ikechangexentrick/function_generator/function_generator/function_generator_ui.cpp

#include "function_generator_ui.h"
#include "Display_OLED.h"

#include "euclidean.h"

static constexpr size_t N_CH = 4096;

extern Application *app;
extern MenuApp app_menu;
extern Display_OLED display;

extern ChannelApp app_channel;
extern ChannelApp app_cv_channel;

extern FreqApp app_freq;

extern SrcApp app_src;
extern MultApp app_mult;
extern PhaseApp app_phase;

extern FuncApp app_func;
extern ARE_Attack_App app_func_are_attack;
extern ARE_Release_App app_func_are_release;

extern PolarityApp app_pol;

extern PatternController ptnctl;
extern Euclid_Len_App app_euc_len;
extern Euclid_Num_App app_euc_num;
extern Euclid_Sft_App app_euc_sft;

void FreqApp::set_sync_mode(size_t ch, SyncType type)
{
	auto &flag = data[ch].sync_flag;
	flag = type;
	register_update();
}

void FreqApp::set_free_mode(size_t ch)
{
	auto &flag = data[ch].sync_flag;
	flag = Free;
	register_update();
}

bool FreqApp::check_new_period(size_t ch, unsigned long t)
{
	bool ret = false;
	unsigned long cur_phase = 0;

	if (sync_mode(ch) != Free) {
		auto coeff = app_mult.get_coeff(ch);
		auto factor = app_phase.get_factor(ch);
		auto freq = get_frequency(ch);
		cur_phase = (t - (unsigned long)(1e6/freq/8.0*factor)) % (unsigned long)(1e6/freq/coeff);
	} else {
		cur_phase = t % (unsigned long)(1e6/get_frequency(ch));
	}

	if (cur_phase < data[ch].prev_phase) ret = true;
	data[ch].prev_phase = cur_phase;
	return ret;
}

void FreqApp::onButton(int state)
{
	if (state == 1) {
		app = &app_menu;

		display.show_app_msg(" ");
		display.show_menu(app_menu.get_current()->get_title());
	}
}

void FreqApp::onRotarySW(RotarySwitch::RSW_DIR dir)
{
	const auto ch = app_channel.get_current_channel();

	if (freq_mode == FREQ_MODE) {
		auto &freq = data[ch].freq;
		if (dir == RotarySwitch::CW) {
			if (freq < 1) {
				freq *= 1.2;
			} else {
				freq += 1;
			}

		} else {
			if (freq <= 1) {
				freq /= 1.2;
			} else {
				freq -= 1;
			}

		}

		display.show_app_msg("   %5.1f", freq);
	} else if (freq_mode == BPM_MODE) {
		size_t bpm = (size_t)(60.0*data[ch].freq);
		if (dir == RotarySwitch::CW) {
			bpm += 1;

		} else {
			if (bpm > 0) {
				bpm -= 1;
			}

		}

		display.show_app_msg("   %3d", bpm);
		data[ch].freq = (double)bpm/60.0;
	} else {
		// never reach here
	}
	register_update();
}

void FreqApp::apply_cv(size_t ch, size_t cv)
{
	auto &freq = data[ch].freq;

	// 0.03 - 30 Hz / -1.5 - 1.5
	auto new_value = pow(10.0, -1.5 + (1.5 - (-1.5))*(double)cv/1024.0);
	freq = new_value;
}

void FreqApp::set_param(size_t ch, double f, unsigned long p)
{
		auto coeff = app_mult.get_coeff(ch);
		if (coeff >= 1) {
			auto &ext_freq = data[ch].ext_freq;
			auto &ext_phase = data[ch].ext_phase;
			ext_freq = f;
			ext_phase = p;
		} else {
			if (data[ch].phase_counter >= 1.0/coeff-1) {
				data[ch].phase_counter = 0;
				auto &ext_freq = data[ch].ext_freq;
				auto &ext_phase = data[ch].ext_phase;
				ext_freq = f;
				ext_phase = p;
			}
			data[ch].phase_counter += 1;
		}
}

void FuncApp::onButton(int state)
{
	if (state == 1) {
		app = &app_menu;

		display.show_app_msg(" ");
		display.show_menu(app_menu.get_current()->get_title());
	}
}

double func_sin(unsigned long t, double freq, unsigned long phase)
{
	return sin( 2*3.141592*freq/1e6*(t - phase) );
}

double func_saw(unsigned long t, double freq, unsigned long phase)
{
	auto lambda = (1e6/freq); // in us
	auto out = (N_CH-1)/lambda * (double)( (t-phase) % (unsigned long)lambda );
	return out;
}

double func_tri(unsigned long t, double freq, unsigned long phase)
{
	auto saw2 = func_saw(t, freq, phase)*2;
	if (saw2 > (N_CH-1)) return (N_CH-1)*2-saw2;
	else return saw2;
}

double func_sq(unsigned long t, double freq, unsigned long phase)
{
	auto saw = func_saw(t, freq, phase);
	return (saw < N_CH/2) ? (N_CH-1) : 0;
}

double func_are(unsigned long t, double freq, unsigned long phase, unsigned long attack, unsigned long release)
{
	auto lambda = (1e6/freq); // in us
	auto l_attack = lambda*attack/100;
	auto l_release = lambda*release/100;

	auto dt = (t-phase) % (unsigned long)lambda;
	if (dt <= l_attack) return (N_CH-1)/l_attack * (double)dt;
	else if (dt <= l_attack+l_release) return (N_CH-1) -(N_CH-1)/l_release * (double)(dt - l_attack);
	else return 0.0;
}

void FuncApp::onRotarySW(RotarySwitch::RSW_DIR dir)
{
	const auto ch = app_channel.get_current_channel();
	auto &idx = data[ch].idx;
	if (dir == RotarySwitch::CW) {
		if (idx < FUNC_MAX-1) idx += 1;

	} else {
		if (idx > 0) idx -= 1;

	}

	display.show_app_msg("   %s", get_func_name(ch));
	register_update();
}

auto FuncApp::get_function(size_t ch) const -> std::function<double(unsigned long, double, unsigned long)>
{
	const auto &idx = data[ch].idx;

	if (idx == SIN) {
		return [=](unsigned long t, double f, unsigned long p) { return (func_sin(
			t, f, p)+1)/2*(N_CH-1); };
	} else if (idx == SAW_TOOTH) {
		return [=](unsigned long t, double f, unsigned long p) { return func_saw(
			t, f, p); };
	} else if (idx == TRIANGLE) {
		return [=](unsigned long t, double f, unsigned long p) { return func_tri(
			t, f, p); };
	} else if (idx == SQUARE) {
		return [=](unsigned long t, double f, unsigned long p) { return func_sq(
			t, f, p); };
	} else if (idx == AR_ENVELOPE) {
		return [=](unsigned long t, double f, unsigned long p) { return func_are(
			t, f, p, app_func_are_attack.get_value(ch), app_func_are_release.get_value(ch)); };
	}

	return std::function<long(unsigned long, double, unsigned long)>();
}

void FuncApp::apply_cv(size_t ch, size_t cv)
{
	auto &idx = data[ch].idx;

	// 0 - FUNC_MAX-1
	idx = (int)(((double)cv/1024.0)*(double)FUNC_MAX);
}

//  -----------------------------------------------

void ChannelApp::onButton(int state)
{
	if (state == 1) {
		app = &app_menu;

		display.show_app_msg(" ");
		display.show_menu(app_menu.get_current()->get_title());
	}
}

void ChannelApp::onRotarySW(RotarySwitch::RSW_DIR dir)
{
	if (dir == RotarySwitch::CW) {
		if (ch < ChannelMax-1) ch += 1;

	} else {
		if (ch > 0) ch -= 1;

	}

	display.show_app_msg("   %u", get_current_channel()+1);
	register_update();
}

//  -----------------------------------------------

void SrcApp::onButton(int state)
{
	if (state == 1) {
		app = &app_menu;

		display.show_app_msg(" ");
		display.show_menu(app_menu.get_current()->get_title());
	}
}

void SrcApp::onRotarySW(RotarySwitch::RSW_DIR dir)
{
	const size_t ch = app_channel.get_current_channel();
	int type = (int)type_print[ch];

	if (dir == RotarySwitch::CW) {
		if (type < FreqApp::Sync_ExtClock) {
			type += 1;
		}
	} else {
		if (type > FreqApp::Sync_Channel1) {
			type -= 1;
		}
	}
	type_print[ch] = (FreqApp::SyncType)type;

	// check if the master channel is external or free or not the channel itself
	if (ch == type || (type < ChannelApp::ChannelMax && app_freq.sync_mode(type) != FreqApp::Free)) {
		display.show_app_msg("   -");
	} else {
		app_freq.set_sync_mode(ch, (FreqApp::SyncType)type);
		display.show_app_msg("   %s", get_source_name((FreqApp::SyncType)type));
	}
	register_update();
}

const char *get_source_name(FreqApp::SyncType type)
{
	if (type == FreqApp::Sync_Channel1) return "ch1";
	else if (type == FreqApp::Sync_Channel2) return "ch2";
	else if (type == FreqApp::Sync_Channel3) return "ch3";
	else if (type == FreqApp::Sync_Channel4) return "ch4";
	else if (type == FreqApp::Sync_Channel5) return "ch5";
	else if (type == FreqApp::Sync_Channel6) return "ch6";
	else if (type == FreqApp::Sync_Channel7) return "ch7";
	else if (type == FreqApp::Sync_Channel8) return "ch8";
	else if (type == FreqApp::Sync_ExtClock) return "clk";
	else return "free";
}

//  -----------------------------------------------

void MultApp::onButton(int state)
{
	if (state == 1) {
		app = &app_menu;

		display.show_app_msg(" ");
		display.show_menu(app_menu.get_current()->get_title());
	}
}

void MultApp::onRotarySW(RotarySwitch::RSW_DIR dir)
{
	const size_t ch = app_channel.get_current_channel();
	auto &sign = data[ch].sign;
	auto &factor = data[ch].factor;

	if (dir == RotarySwitch::CW) {
		if (sign == Mult) {
			factor += 1;
		} else if (sign == Eq) {
			factor += 1;
			sign = Mult;
		} else {
			factor -= 1;
			if (factor == 1) {
				sign = Eq;
			}
		}

	} else {
		if (sign == Div) {
			factor += 1;
		} else if (sign == Eq) {
			factor += 1;
			sign = Div;
		} else {
			factor -= 1;
			if (factor == 1) {
				sign = Eq;
			}
		}

	}

	display.show_app_msg("   %s%d", get_sign(ch), get_factor(ch));
	register_update();
}

void MultApp::apply_cv(size_t ch, size_t cv)
{
	auto &factor = data[ch].factor;
	auto &sign = data[ch].sign;

	// /10 - *10
	auto x = (double)(cv-512)/1024.0;
	if (x >= -0.05 || x <= 0.05) {
		sign = Eq;
		factor = 1;
	} else if (x > 0.05) {
		sign = Mult;
		factor = (int)(x*20);
	} else if (x < -0.05) {
		sign = Div;
		factor = (int)(-x*20);
	}
}

double MultApp::get_coeff(size_t ch) const
{
	const auto &sign = data[ch].sign;
	const auto &factor = data[ch].factor;
	if (sign == Mult || sign == Eq) return factor;
	else return 1.0/factor;
}

//  -----------------------------------------------

void PhaseApp::onButton(int state)
{
	if (state == 1) {
		app = &app_menu;

		display.show_app_msg(" ");
		display.show_menu(app_menu.get_current()->get_title());
	}
}

void PhaseApp::onRotarySW(RotarySwitch::RSW_DIR dir)
{
	const size_t ch = app_channel.get_current_channel();
	auto &factor = data[ch].factor;

	if (dir == RotarySwitch::CW) {
		if (factor < 8) factor += 1;

	} else {
		if (factor > 0) factor -= 1;

	}

	display.show_app_msg("   %d", get_factor(ch));
	register_update();
}

void PhaseApp::apply_cv(size_t ch, size_t cv)
{
	auto &factor = data[ch].factor;

	// 0 - 8
	factor = (int)((double)cv/1024.0*8);
}

//  -----------------------------------------------

void ARE_Attack_App::onButton(int state)
{
	if (state == 1) {
		app = &app_menu;

		display.show_app_msg(" ");
		display.show_menu(app_menu.get_current()->get_title());
	}
}

void ARE_Attack_App::onRotarySW(RotarySwitch::RSW_DIR dir)
{
	const size_t ch = app_channel.get_current_channel();
	auto &value = data[ch].value;
	const auto &release = app_func_are_release.get_value(ch);

	if (dir == RotarySwitch::CW) {
		if (value + release < 100) value += 1;
	} else {
		if (value > 1) value -= 1;
	}

	display.show_app_msg("   %d", value);
	register_update();
}

void ARE_Attack_App::apply_cv(size_t ch, size_t cv)
{
	auto &value = data[ch].value;

	// 0 - 100-release
	const auto release = app_func_are_release.get_value(ch);
	value = (double)cv/1024.0*(double)(100-release);
}

void ARE_Release_App::onButton(int state)
{
	if (state == 1) {
		app = &app_menu;

		display.show_app_msg(" ");
		display.show_menu(app_menu.get_current()->get_title());
	}
}

void ARE_Release_App::onRotarySW(RotarySwitch::RSW_DIR dir)
{
	const size_t ch = app_channel.get_current_channel();
	auto &value = data[ch].value;
	const auto &attack = app_func_are_attack.get_value(ch);

	if (dir == RotarySwitch::CW) {
		if (value + attack < 100) value += 1;
	} else {
		if (value > 1) value -= 1;
	}

	display.show_app_msg("   %d", value);
	register_update();
}

void ARE_Release_App::apply_cv(size_t ch, size_t cv)
{
	auto &value = data[ch].value;

	// 0 - 100-attack
	const auto attack = app_func_are_attack.get_value(ch);
	value = (double)cv/1024.0*(double)(100-attack);
}

//  -----------------------------------------------

void PolarityApp::onButton(int state)
{
	if (state == 1) {
		app = &app_menu;

		display.show_app_msg(" ");
		display.show_menu(app_menu.get_current()->get_title());
	}
}

void PolarityApp::onRotarySW(RotarySwitch::RSW_DIR dir)
{
	const size_t ch = app_channel.get_current_channel();
	auto &value = data[ch].mode;

	if (dir == RotarySwitch::CW) {
		if (value == Unipolar) value = Bipolar;
	} else {
		if (value == Bipolar) value = Unipolar;
	}

	display.show_app_msg("   %s", get_mode_msg(ch));
	register_update();
}


//  -----------------------------------------------

void PatternController::notify(size_t ch)
{
	auto type = data[ch].type;

	if (type == Off) {
		data[ch].enabled = true;
	} else if (type == Euclidean) {

		const auto len = app_euc_len.get_value(ch);

		auto &cnt = data[ch].euc_cnt;
		int *ptn = data[ch].euc_pattern;
		if (cnt == 0) {
			auto num = app_euc_num.get_value(ch);
			auto sft = app_euc_sft.get_value(ch);
			if (num > len) {
				num = len;
				app_euc_num.set_value(ch, num);
			}
			if (sft > len) {
				sft = len;
				app_euc_sft.set_value(ch, sft);
			}
			euclidean(num, sft, ptn, len);
		}

		if (ptn[cnt]) data[ch].enabled = true;
		else data[ch].enabled = false;

		if (++cnt >= len) cnt = 0;
	}
}

bool PatternController::enabled(size_t ch) const
{
	return data[ch].enabled;
}

void PatternController::get_msg(size_t ch, char *p, size_t len)
{
	if (data[ch].type == Off) {
		snprintf(p, len, "  ptn:off");
	} else if (data[ch].type == Euclidean) {
		snprintf(p, len, "  ptn:Euc:%d/%d/%d", app_euc_len.get_value(ch), app_euc_num.get_value(ch), app_euc_sft.get_value(ch));
	}
}

void Euclid_Len_App::onButton(int state)
{
	if (state == 1) {
		app = &app_menu;

		display.show_app_msg(" ");
		display.show_menu(app_menu.get_current()->get_title());
	}
}

void Euclid_Len_App::onRotarySW(RotarySwitch::RSW_DIR dir)
{
	const size_t ch = app_channel.get_current_channel();
	auto &value = data[ch].value;

	if (dir == RotarySwitch::CW) {
		if (value < MAX_LEN) value += 1;
	} else {
		if (value > 1) value -= 1;
	}

	display.show_app_msg("   %d", value);
	register_update();
}

void Euclid_Len_App::apply_cv(size_t ch, size_t cv)
{
	auto &value = data[ch].value;

	// 1 - MAX_LEN-1
	value = (int)((double)cv/1024.0*(double)(MAX_LEN-1)) +1;
}

void Euclid_Num_App::onButton(int state)
{
	if (state == 1) {
		app = &app_menu;

		display.show_app_msg(" ");
		display.show_menu(app_menu.get_current()->get_title());
	}
}

void Euclid_Num_App::onRotarySW(RotarySwitch::RSW_DIR dir)
{
	const size_t ch = app_channel.get_current_channel();
	auto &value = data[ch].value;
	const auto len = app_euc_len.get_value(ch);

	if (dir == RotarySwitch::CW) {
		if (value < len) value += 1;
	} else {
		if (value > 0) value -= 1;
	}

	display.show_app_msg("   %d", value);
	register_update();
}

void Euclid_Num_App::apply_cv(size_t ch, size_t cv)
{
	auto &value = data[ch].value;

	// 0 - len
	const auto len = app_euc_len.get_value(ch);
	value = (int)((double)cv/1024.0*(double)len);
}

void Euclid_Sft_App::onButton(int state)
{
	if (state == 1) {
		app = &app_menu;

		display.show_app_msg(" ");
		display.show_menu(app_menu.get_current()->get_title());
	}
}

void Euclid_Sft_App::onRotarySW(RotarySwitch::RSW_DIR dir)
{
	const size_t ch = app_channel.get_current_channel();
	auto &value = data[ch].value;
	const auto len = app_euc_len.get_value(ch);

	if (dir == RotarySwitch::CW) {
		if (value < len) value += 1;
	} else {
		if (value > 0) value -= 1;
	}

	display.show_app_msg("   %d", value);
	register_update();
}

void Euclid_Sft_App::apply_cv(size_t ch, size_t cv)
{
	auto &value = data[ch].value;

	// 0 - len
	const auto len = app_euc_len.get_value(ch);
	value = (int)((double)cv/1024.0*(double)len);
}


template class CVApp<11>;

template <int N>
void CVApp<N>::onButton(int state)
{
	if (state == 1) {

		if (this->idx == this->titles.size()-1) /* Back */ {
			app = &app_menu;

			display.show_app_msg(" ");
			display.show_menu(app_menu.get_current()->get_title());

		} else {
			this->selected = this->idx;
			this->callbacks[this->idx]();

		}
	}
}

template <int N>
void CVApp<N>::onRotarySW(RotarySwitch::RSW_DIR dir)
{
	if (dir == RotarySwitch::CW) {
		if (this->idx < this->titles.size()-1) this->idx += 1;
	} else {
		if (this->idx > 0) this->idx -= 1;
	}

	const auto &item = this->titles[this->idx].c_str();

	if (this->idx == this->titles.size()-1) {
		display.show_app_msg("   <%s", item);
	} else {
		display.show_app_msg("   [%s]", item);
	}
	register_update();
}

template <int N>
void CVApp<N>::get_app_msg(char *p, size_t len)
{
	memcpy(p, &this->titles[this->selected][0], len);
}

//  -----------------------------------------------

void Menu_Channel::exec()
{
	display.show_app_msg("   %u", app_channel.get_current_channel()+1);
	app = &app_channel;
}


void Menu_Free::exec()
{
	const size_t ch = app_channel.get_current_channel();
	app_freq.set_free_mode(ch);
}

void Menu_Freq::exec()
{
	const size_t ch = app_channel.get_current_channel();
	display.show_app_msg("   %5.1f", app_freq.get_frequency(ch));
	app_freq.set_mode(FreqApp::FREQ_MODE);
	app = &app_freq;
}

void Menu_BPM::exec()
{
	const size_t ch = app_channel.get_current_channel();
	display.show_app_msg("   %3d", app_freq.get_bpm(ch));
	app_freq.set_mode(FreqApp::BPM_MODE);
	app = &app_freq;
}


void Menu_Sync::exec()
{
}

void Menu_Src::exec()
{
	const auto ch = app_channel.get_current_channel();
	const auto type = app_freq.sync_mode(ch);
	display.show_app_msg("   %s", get_source_name(type));
	app = &app_src;
}

void Menu_Mult::exec()
{
	const size_t ch = app_channel.get_current_channel();
	display.show_app_msg("   %s%d", app_mult.get_sign(ch), app_mult.get_factor(ch));
	app = &app_mult;
}

void Menu_Phase::exec()
{
	const size_t ch = app_channel.get_current_channel();
	display.show_app_msg("   %d", app_phase.get_factor(ch));
	app = &app_phase;
}


void Menu_Func::exec()
{
}

void Menu_Func_sin::exec()
{
	const size_t ch = app_channel.get_current_channel();
	app_func.set_function(ch, SIN);
}

void Menu_Func_saw::exec()
{
	const size_t ch = app_channel.get_current_channel();
	app_func.set_function(ch, SAW_TOOTH);
}

void Menu_Func_tri::exec()
{
	const size_t ch = app_channel.get_current_channel();
	app_func.set_function(ch, TRIANGLE);
}

void Menu_Func_sq::exec()
{
	const size_t ch = app_channel.get_current_channel();
	app_func.set_function(ch, SQUARE);
}

void Menu_Func_ARE::exec()
{
	const size_t ch = app_channel.get_current_channel();
	app_func.set_function(ch, AR_ENVELOPE);
}

void Menu_Func_ARE_Attack::exec()
{
	const size_t ch = app_channel.get_current_channel();
	display.show_app_msg("   %d", app_func_are_attack.get_value(ch));
	app = &app_func_are_attack;
}

void Menu_Func_ARE_Release::exec()
{
	const size_t ch = app_channel.get_current_channel();
	display.show_app_msg("   %d", app_func_are_release.get_value(ch));
	app = &app_func_are_release;
}


void Menu_Polarity::exec()
{
	const size_t ch = app_channel.get_current_channel();
	display.show_app_msg("   %s", app_pol.get_mode_msg(ch));
	app = &app_pol;
}


void Menu_Pattern::exec()
{
}

void Menu_Pattern_Off::exec()
{
	const size_t ch = app_channel.get_current_channel();
	ptnctl.set_type(ch, PatternController::Off);
}

void Menu_Pattern_Euclidean::exec()
{
	const size_t ch = app_channel.get_current_channel();
	ptnctl.set_type(ch, PatternController::Euclidean);
}

void Menu_Pattern_Euclidean_Length::exec()
{
	const size_t ch = app_channel.get_current_channel();
	display.show_app_msg("   %d", app_euc_len.get_value(ch));
	app = &app_euc_len;
}

void Menu_Pattern_Euclidean_Number::exec()
{
	const size_t ch = app_channel.get_current_channel();
	display.show_app_msg("   %d", app_euc_num.get_value(ch));
	app = &app_euc_num;
}

void Menu_Pattern_Euclidean_Shift::exec()
{
	const size_t ch = app_channel.get_current_channel();
	display.show_app_msg("   %d", app_euc_sft.get_value(ch));
	app = &app_euc_sft;
}


void Menu_CV_Channel::exec()
{
	display.show_app_msg("   %u", cv_app->get_current_channel()+1);
	app = cv_app;
}

void Menu_CV::exec()
{
	char msg[16];
	memset(msg, 0, 16);
	cv_app->get_app_msg(msg, 16);
	display.show_app_msg("   %s", msg);
	app = cv_app;
}
